grafmar/Arduino-Reflow-Oven/src/ReflowOven/TouchButton.cpp

#include "TouchButton.h"
#include "ReflowOven.h"

const PROGMEM TouchButton::TouchButtonElement TouchButton::TOUCH_BUTTONS[TouchButton::NUM_OF_TOUCH_BUTTONS] = {
    { Display::homeScreen,             0, 106, 200, 240, TouchButton::buttonSettings },
    { Display::homeScreen,           106, 213, 200, 240, TouchButton::buttonStartStopReset },
    { Display::homeScreen,           213, 320, 200, 240, TouchButton::buttonAboutInfo },
    
    { Display::settingsScreen,         0,  54, 200, 240, TouchButton::buttonBack },
    { Display::settingsScreen,        54, 142, 200, 240, TouchButton::buttonEdit },
    { Display::settingsScreen,       142, 231, 200, 240, TouchButton::buttonLoad },
    { Display::settingsScreen,       231, 320, 200, 240, TouchButton::buttonSave },

    { Display::editSetpointsScreen,    0,  54, 200, 240, TouchButton::buttonBackSettings },
    { Display::editSetpointsScreen,   54, 107, 200, 240, TouchButton::buttonP1 },
    { Display::editSetpointsScreen,  107, 161, 200, 240, TouchButton::buttonP2 },
    { Display::editSetpointsScreen,  161, 214, 200, 240, TouchButton::buttonP3 },
    { Display::editSetpointsScreen,  214, 268, 200, 240, TouchButton::buttonP4 },
    { Display::editSetpointsScreen,  268, 320, 200, 240, TouchButton::buttonP5 },

    { Display::loadSetpointsScreen,    0, 320,   0,  40, TouchButton::buttonM1 },
    { Display::loadSetpointsScreen,    0, 320,  40,  80, TouchButton::buttonM2 },
    { Display::loadSetpointsScreen,    0, 320,  80, 120, TouchButton::buttonM3 },
    { Display::loadSetpointsScreen,    0, 320, 120, 160, TouchButton::buttonM4 },
    { Display::loadSetpointsScreen,    0, 320, 160, 200, TouchButton::buttonM5 },
    { Display::loadSetpointsScreen,   54, 320, 200, 240, TouchButton::buttonDefault },
    { Display::loadSetpointsScreen,    0,  54, 200, 240, TouchButton::buttonBackSettings },

    { Display::saveSetpointsScreen,    0, 320,   0,  40, TouchButton::buttonM1 },
    { Display::saveSetpointsScreen,    0, 320,  40,  80, TouchButton::buttonM2 },
    { Display::saveSetpointsScreen,    0, 320,  80, 120, TouchButton::buttonM3 },
    { Display::saveSetpointsScreen,    0, 320, 120, 160, TouchButton::buttonM4 },
    { Display::saveSetpointsScreen,    0, 320, 160, 200, TouchButton::buttonM5 },
    { Display::saveSetpointsScreen,   54, 320, 200, 240, TouchButton::buttonDefault },
    { Display::saveSetpointsScreen,    0,  54, 200, 240, TouchButton::buttonBackSettings },

    { Display::enterNameScreen,      231, 320, 200, 240, TouchButton::buttonSaveAs },
    { Display::enterNameScreen,        0,  54, 200, 240, TouchButton::buttonBackSettings },

    { Display::setpointInputScreen,   0,  80,  90, 140, TouchButton::button1 },
    { Display::setpointInputScreen,  80, 160,  90, 140, TouchButton::button2 },
    { Display::setpointInputScreen, 160, 240,  90, 140, TouchButton::button3 },
    { Display::setpointInputScreen,   0,  80, 140, 190, TouchButton::button4 },
    { Display::setpointInputScreen,  80, 160, 140, 190, TouchButton::button5 },
    { Display::setpointInputScreen, 160, 240, 140, 190, TouchButton::button6 },
    { Display::setpointInputScreen,   0,  80, 190, 240, TouchButton::button7 },
    { Display::setpointInputScreen,  80, 160, 190, 240, TouchButton::button8 },
    { Display::setpointInputScreen, 160, 240, 190, 240, TouchButton::button9 },
    { Display::setpointInputScreen, 240, 320,  90, 140, TouchButton::buttonDel },
    { Display::setpointInputScreen, 240, 320, 140, 190, TouchButton::button0 },
    { Display::setpointInputScreen, 240, 320, 190, 240, TouchButton::buttonOK },
    { Display::setpointInputScreen,   0,  80,   0,  45, TouchButton::buttonTemp },
    { Display::setpointInputScreen,   0,  80,  45,  90, TouchButton::buttonTime },

    { Display::aboutInfoScreen,    0,  54, 200, 240, TouchButton::buttonBack}
};

TouchButton::TouchButton() :
    // For better pressure precision, we need to know the resistance
    // between X+ and X- Use any multimeter to read it
    // For the one we're using, its 300 ohms across the X plate
    ts(XP, YP, XM, YM, 300)
{
}

TouchButton::~TouchButton() {
}

TouchButton::ButtonId TouchButton::getTouchedButton(Display::screen currentScreen) {
    // get touched point
    digitalWrite(13, HIGH);
    TSPoint p = ts.getPoint();
    digitalWrite(13, LOW);
    pinMode(XM, OUTPUT);
    pinMode(YP, OUTPUT);

    // map to display size
    uint16_t x = map(p.y, TS_MINY, TS_MAXY, 0, 320);
    uint16_t y = map(p.x, TS_MINX, TS_MAXX, 240, 0);

    // if touch event
    if (p.z > MINPRESSURE && p.z < MAXPRESSURE) {
        Serial.print(F("Touch: "));
        Serial.print(x, DEC);
        Serial.print(F(", "));
        Serial.println(y, DEC);

        for (uint16_t i=0; i < NUM_OF_TOUCH_BUTTONS; i++) {
            TouchButtonElement actualTouchButton;
            memcpy_P(&actualTouchButton, &TOUCH_BUTTONS[i], sizeof(actualTouchButton));
            if (actualTouchButton.screen == currentScreen) {
                if ((x > actualTouchButton.x1)
                    && (x < actualTouchButton.x2)
                    && (y > actualTouchButton.y1)
                    && (y < actualTouchButton.y2)) {
                
                    return actualTouchButton.buttonId;
                }
            }
        }
    }

    // No touch event, or no button not recognized
    return noButton;
}

char TouchButton::getTouchedKey() {
    // get touched point
    digitalWrite(13, HIGH);
    TSPoint p = ts.getPoint();
    digitalWrite(13, LOW);
    pinMode(XM, OUTPUT);
    pinMode(YP, OUTPUT);

    // map to display size
    uint16_t x = map(p.y, TS_MINY, TS_MAXY, 0, 320);
    uint16_t y = map(p.x, TS_MINX, TS_MAXX, 240, 0);

    char key = 0;
    // if touch event
    if (p.z > MINPRESSURE && p.z < MAXPRESSURE) {
        Serial.print(F("Key-Touch: "));
        Serial.print(x, DEC);
        Serial.print(F(", "));
        Serial.println(y, DEC);

        if ((y > 40) && (y < 200) && (x > 0) && (x < 320)) {
            uint16_t xKey = (x + 2U) / 36U;
            uint16_t yKey = (y - 40U) / 30U;
            uint16_t index = xKey + yKey * 9U;
            Serial.print(F("eval: "));
            Serial.print(xKey, DEC);
            Serial.print(F(", "));
            Serial.print(yKey, DEC);
            Serial.print(F(", "));
            Serial.print(index, DEC);
            if (index >= 44) {
                // no key
            } else if (index >= 42) {
                key = 127; // Del
            } else if (index >= 39) {
                key = ' ';
            } else if (index >= 38) {
                key = '_';
            } else if (index >= 37) {
                key = '.';
            } else if (index >= 38) {
                key = ',';
            } else if (index >= 26) {
                key = '0' + index - 26;
            } else {
                key = 'A' + index;
            }
            Serial.print(F(", "));
            Serial.println(key, DEC);
        }
    }

    return key;
}

bool TouchButton::isTouched() {
    // get touched point
    digitalWrite(13, HIGH);
    TSPoint p = ts.getPoint();
    digitalWrite(13, LOW);
    pinMode(XM, OUTPUT);
    pinMode(YP, OUTPUT);

    bool retval = (p.z > MINPRESSURE && p.z < MAXPRESSURE);
    //Serial.print(F("Touched: "));
    //Serial.println(retval);

    return retval;
}
